bionicbone/Workshop-Environment-Monitor/images/2N2222A Transistor.png

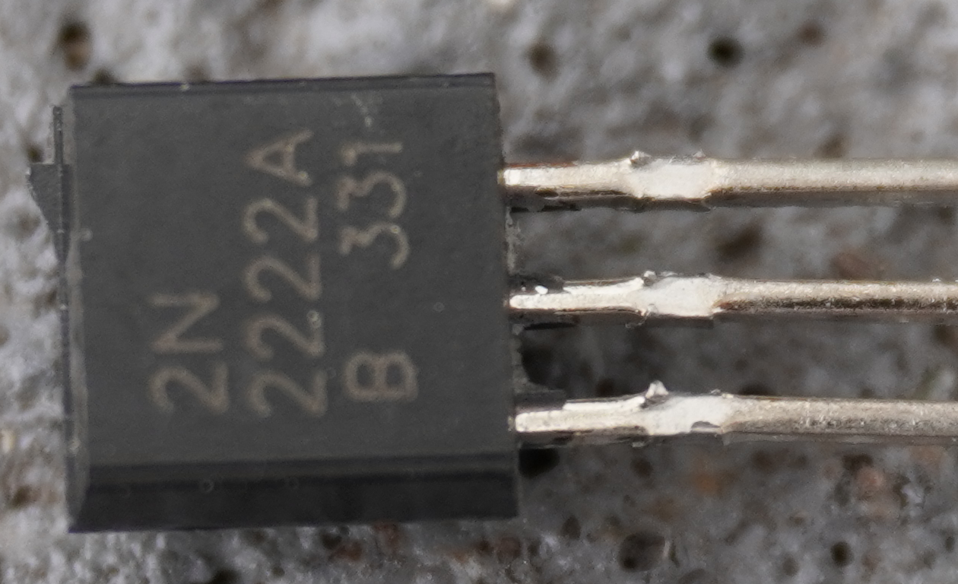
images/2N2222A Transistor.png
