bionicbone/Workshop-Environment-Monitor/images/10k Size 1206 SMD Resistor.png

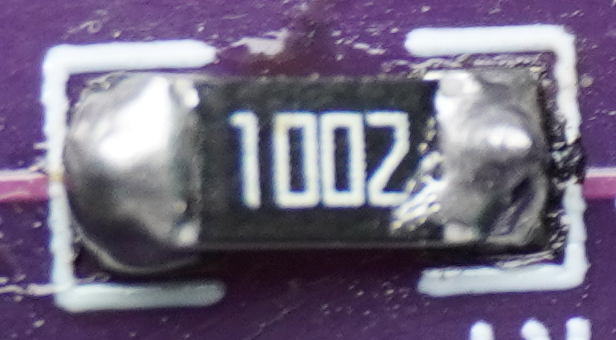
images/10k Size 1206 SMD Resistor.png
