bionicbone/Workshop-Environment-Monitor/images/47uF 50v LowESR Capacitor.png

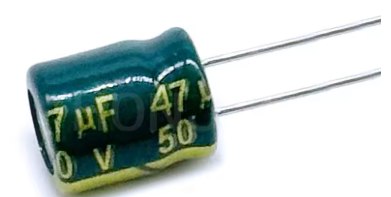
images/47uF 50v LowESR Capacitor.png
