bionicbone/Workshop-Environment-Monitor/images/100uF 25v LowESR Capacitor.png

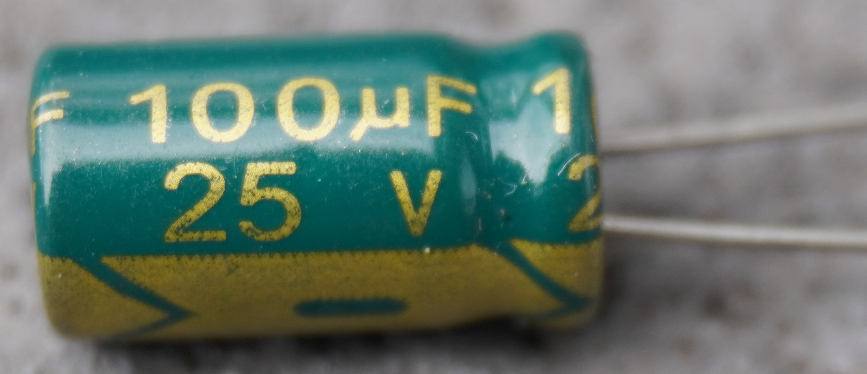
images/100uF 25v LowESR Capacitor.png
