bionicbone/Workshop-Environment-Monitor/images/Adafruit SGP30 ONLY.png

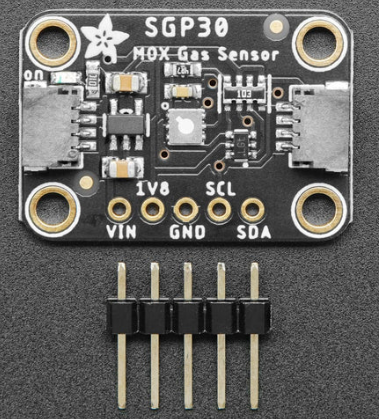
images/Adafruit SGP30 ONLY.png
