bionicbone/Workshop-Environment-Monitor/images/Adafruit SHT40 ONLY.png

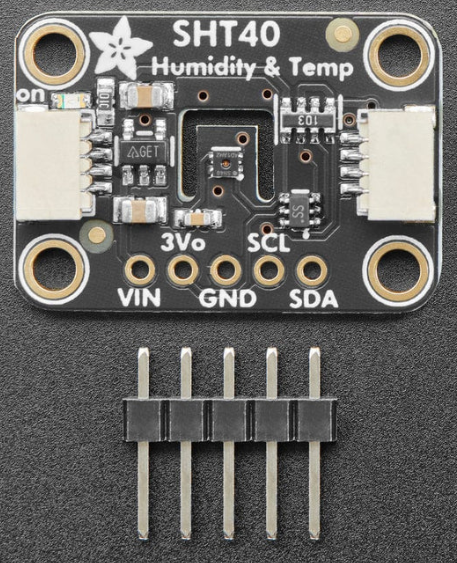
images/Adafruit SHT40 ONLY.png
