bionicbone/Workshop-Environment-Monitor/images/HEADER 2.54 20x2 Female.png

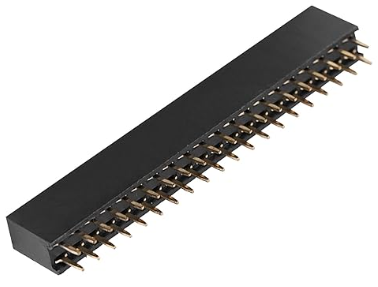
images/HEADER 2.54 20x2 Female.png
