bionicbone/Workshop-Environment-Monitor/images/HEADER 2.54 40x1 Female.png

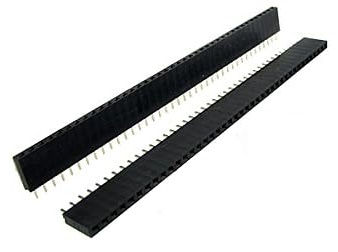
images/HEADER 2.54 40x1 Female.png
