bionicbone/Workshop-Environment-Monitor/images/LD2410B.png

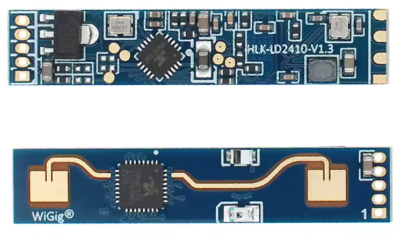
images/LD2410B.png
