bionicbone/Workshop-Environment-Monitor/images/Plantower PMS5003 Particle Sensor ONLY.png

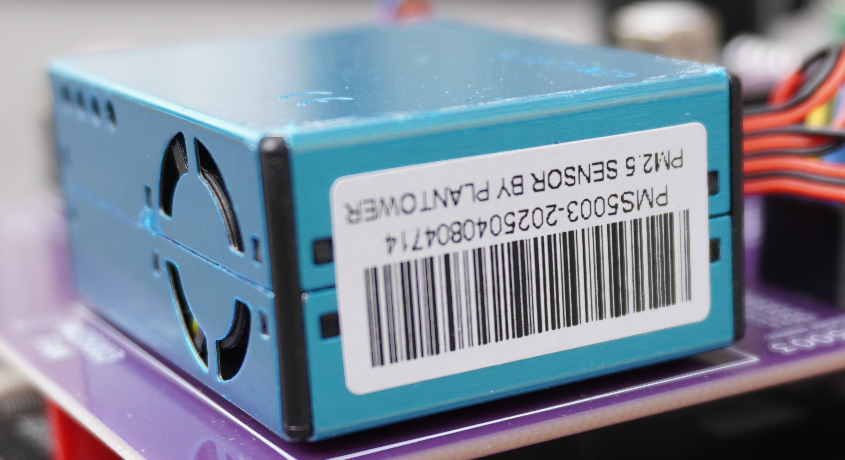
images/Plantower PMS5003 Particle Sensor ONLY.png
