bionicbone/Workshop-Environment-Monitor/images/Power Barrel Jack Connector 2_5mm x 5_5mm.png

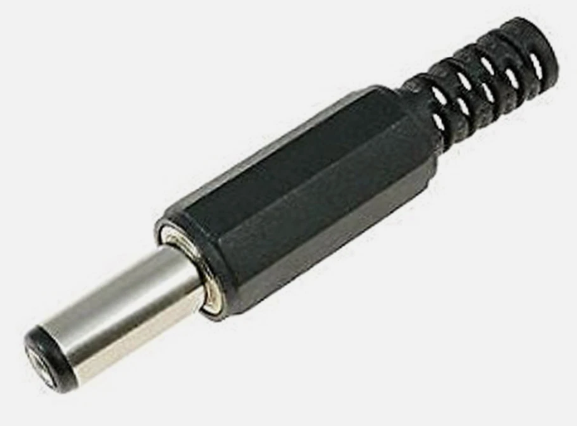
images/Power Barrel Jack Connector 2_5mm x 5_5mm.png
