bionicbone/Workshop-Environment-Monitor/images/SCD40 Breakout Board.png

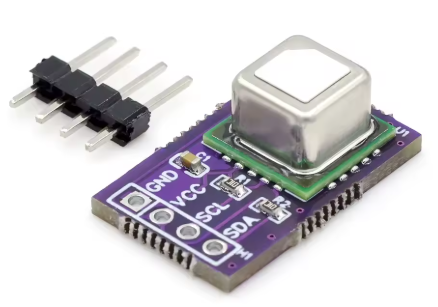
images/SCD40 Breakout Board.png
