bionicbone/Workshop-Environment-Monitor/images/SFA40 Breakout Board.png

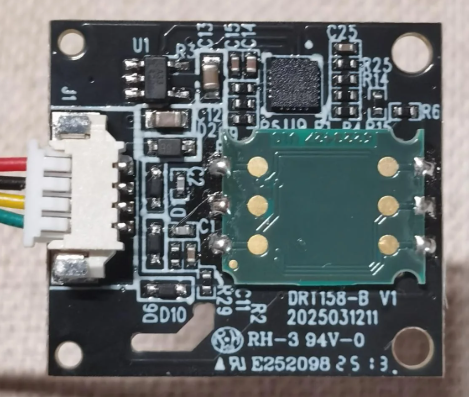
images/SFA40 Breakout Board.png
