bionicbone/Workshop-Environment-Monitor/images/SS34 SMD Schottky Diode.png

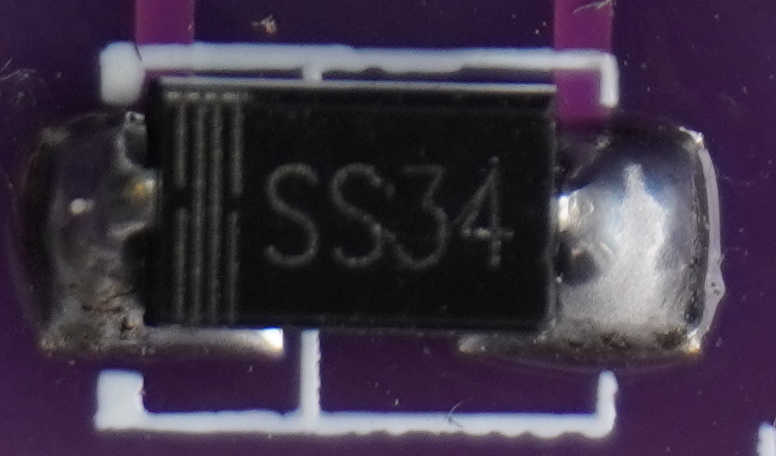
images/SS34 SMD Schottky Diode.png
