bionicbone/Workshop-Environment-Monitor/images/WEM fitted in workshop.JPG

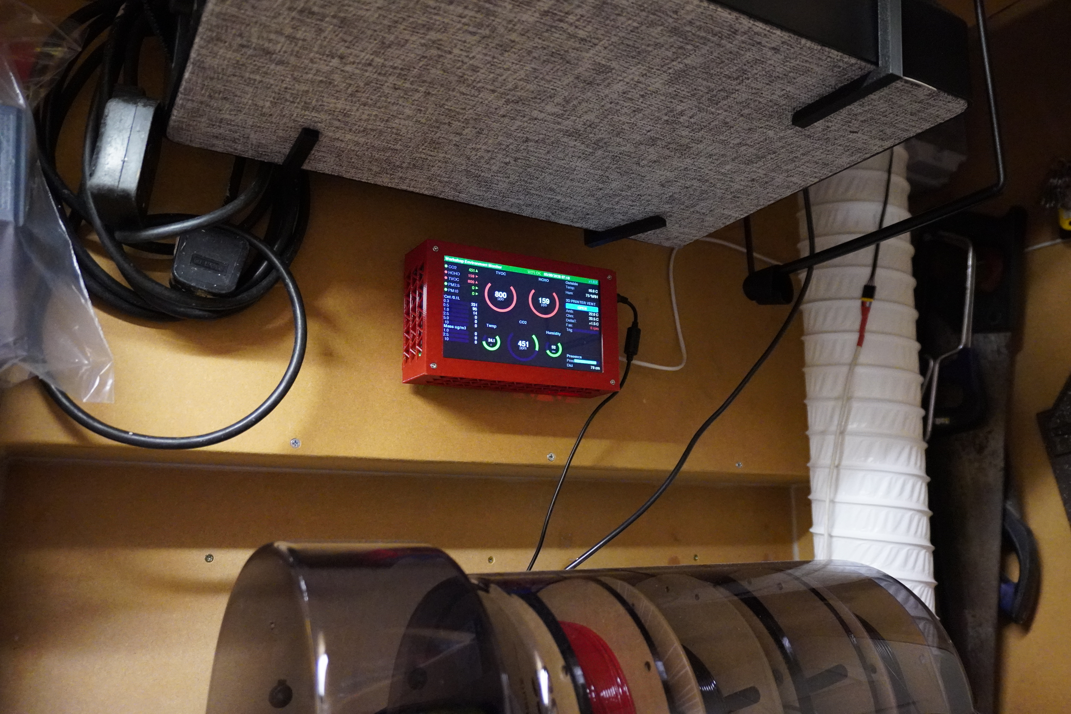
images/WEM fitted in workshop.JPG
