bionicbone/Workshop-Environment-Monitor/images/WEM High Readings.JPG

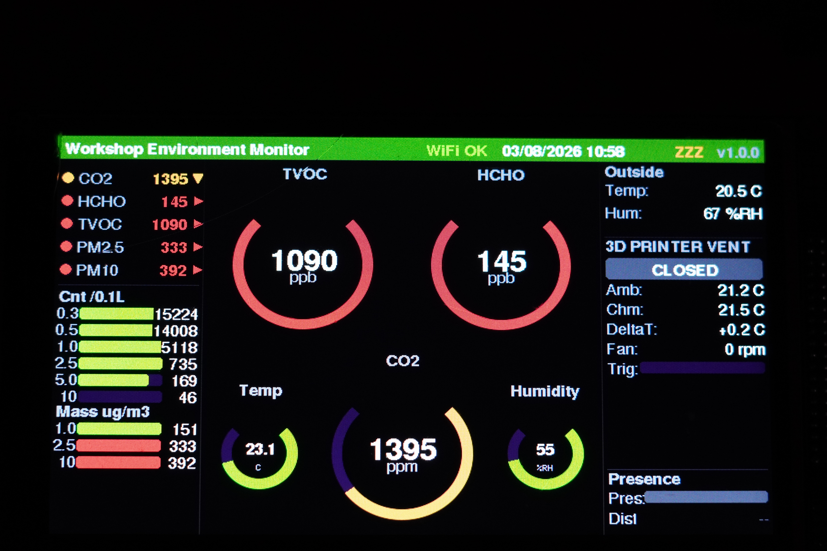
images/WEM High Readings.JPG
