bionicbone/Workshop-Environment-Monitor/images/WEM PCB V1.1 Unpopulated.JPG

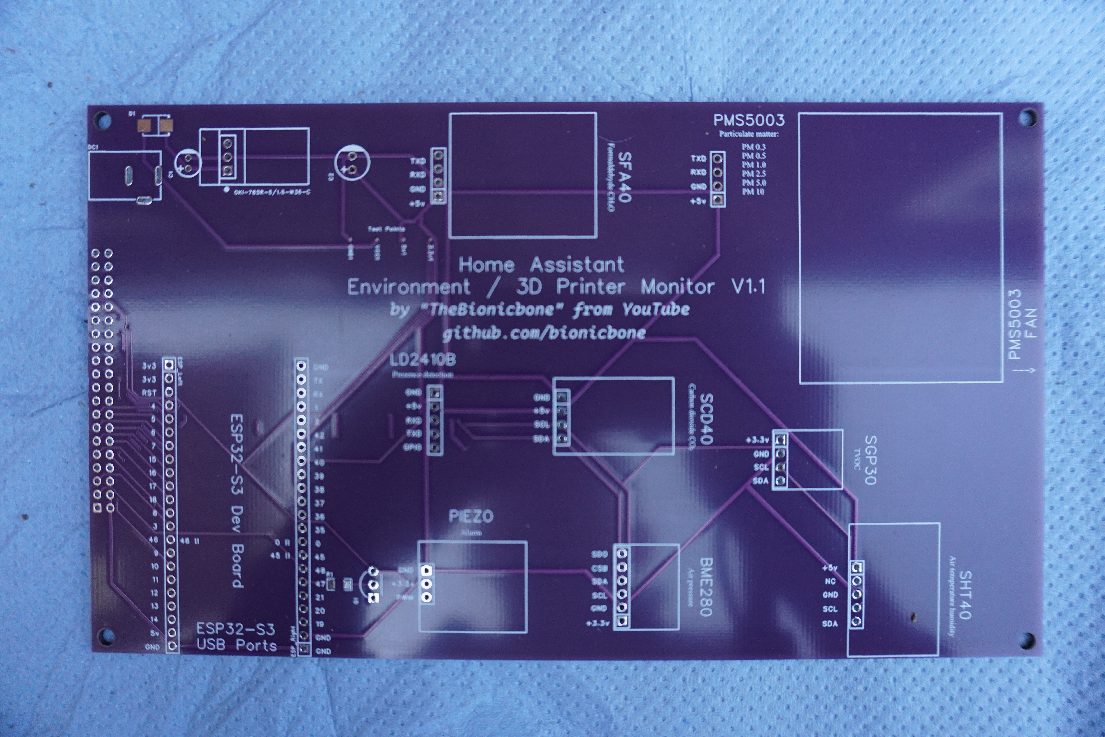
images/WEM PCB V1.1 Unpopulated.JPG
