bionicbone/Workshop-Environment-Monitor/images/7 inch TFT Captive Touch Display with SSD1963 Ordering Details.png

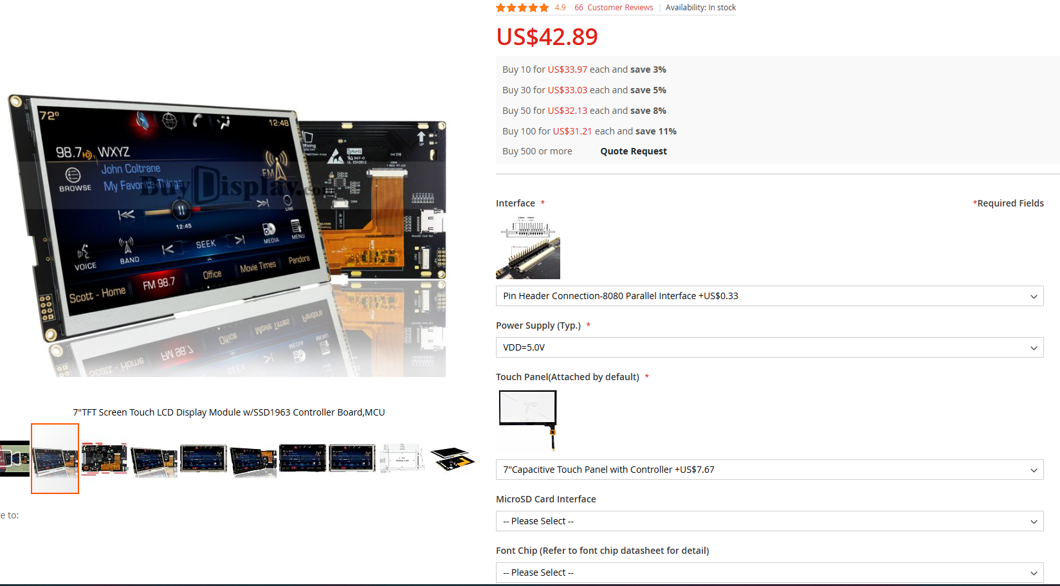
images/7 inch TFT Captive Touch Display with SSD1963 Ordering Details.png
