bionicbone/Workshop-Environment-Monitor/images/PCB Cost from JCLPCB Aug 2026.png

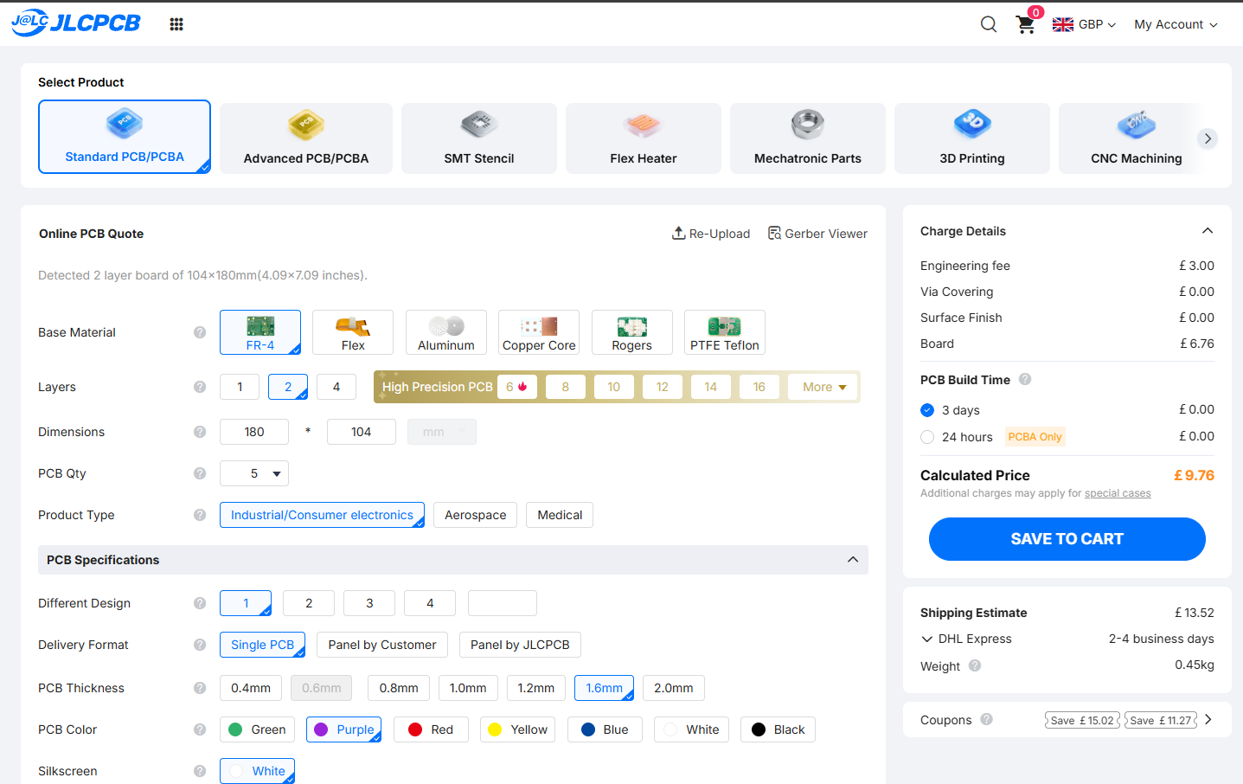
images/PCB Cost from JCLPCB Aug 2026.png
