bionicbone/Workshop-Environment-Monitor/images/SGP30 Supplier SZYTF Issues DO NOT BUY.png

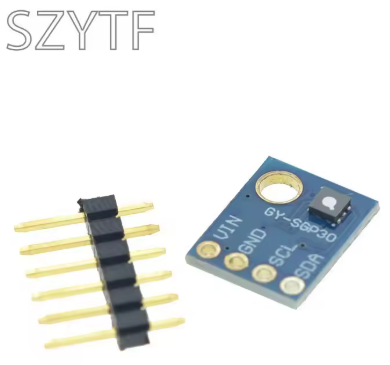
images/SGP30 Supplier SZYTF Issues DO NOT BUY.png
