bionicbone/Workshop-Environment-Monitor/images/USB Power Tested 5v 2A 10W.png

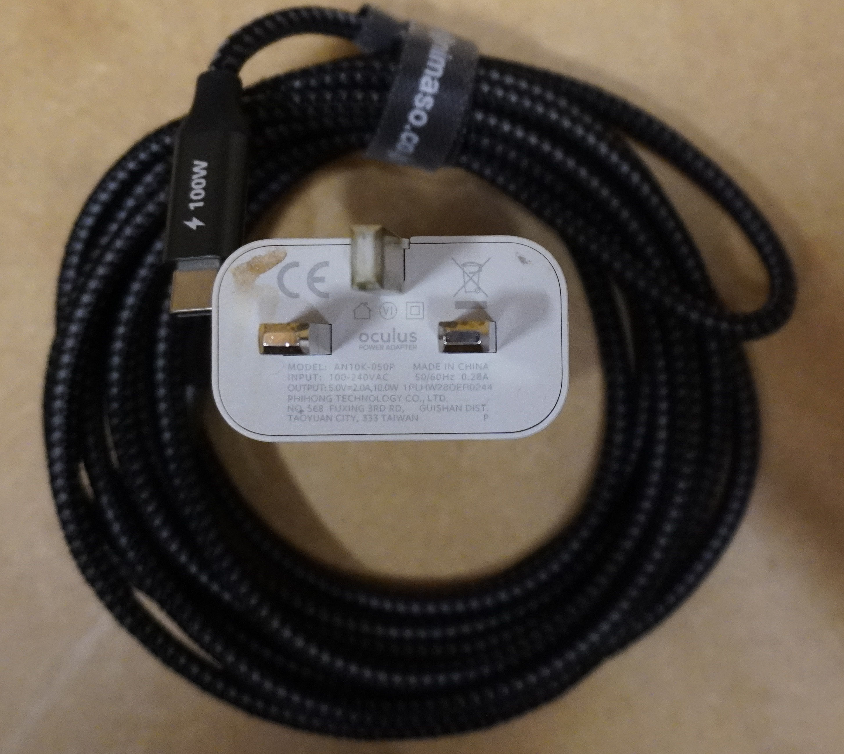
images/USB Power Tested 5v 2A 10W.png
