bionicbone/Workshop-Environment-Monitor/images/Fake Sensirion SGP30 Issues DO NOT BUY.png

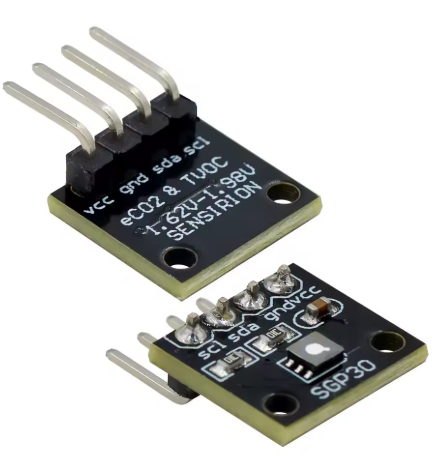
images/Fake Sensirion SGP30 Issues DO NOT BUY.png
